justcallmekoko/ESP32DualBandWardriver/docs/images/GeoFencedScreen1.jpg

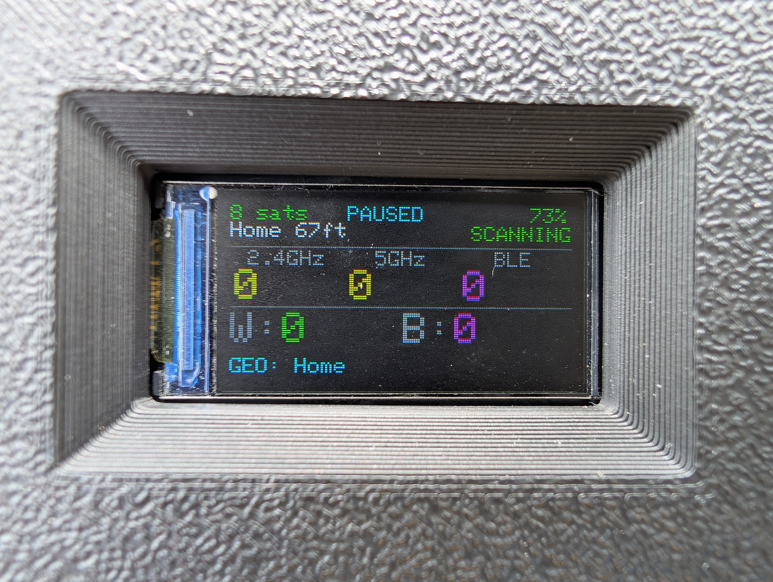
docs/images/GeoFencedScreen1.jpg
