justcallmekoko/ESP32DualBandWardriver/docs/images/WardrivingScreen1.jpg

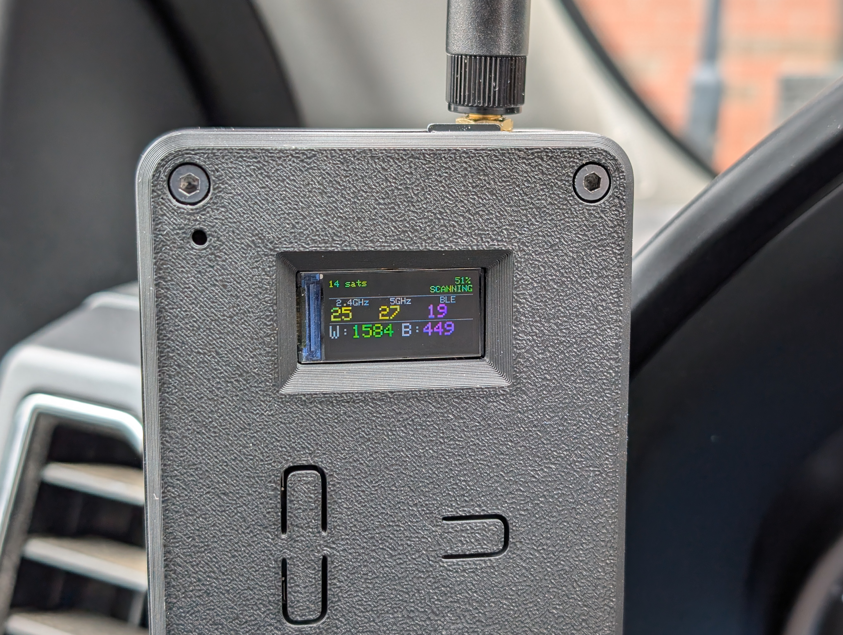
docs/images/WardrivingScreen1.jpg
