justcallmekoko/ESP32DualBandWardriver/docs/images/WebLogScreen.png

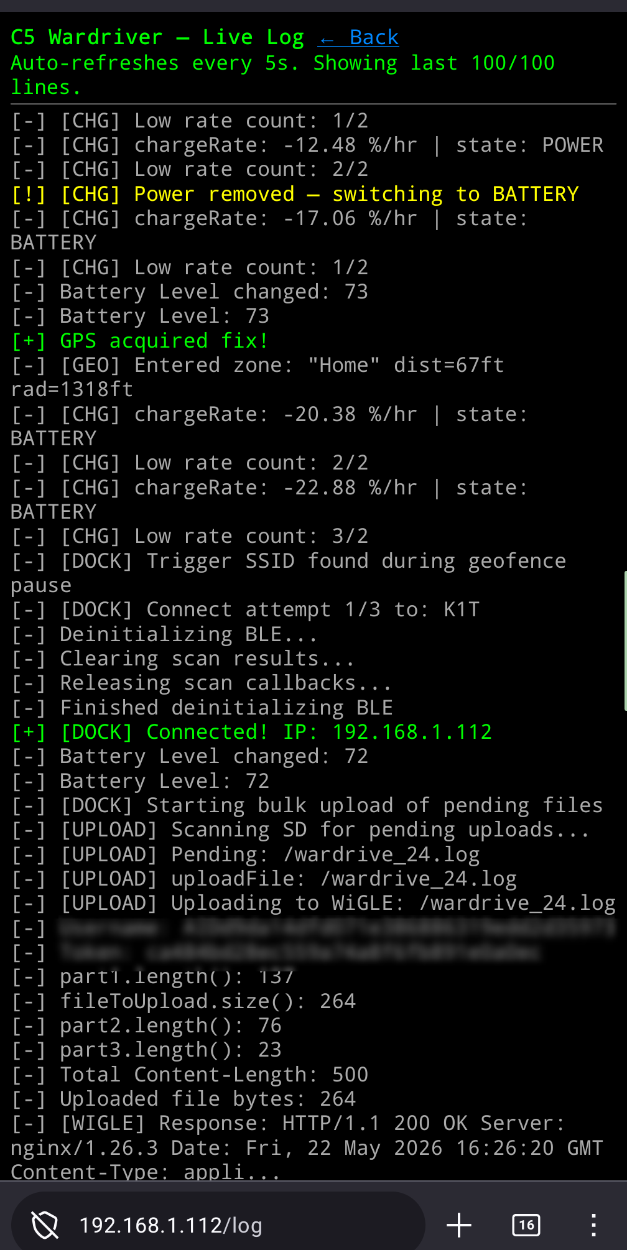
docs/images/WebLogScreen.png
