justcallmekoko/ESP32DualBandWardriver/src/Switches.h

#ifndef Switches_h
#define Switches_h

#include <Arduino.h>
#include "utils.h"

class Switches {
	private:
		int pin;
		uint32_t hold_lim;
		uint32_t cur_hold;
		
		uint32_t hold_init = millis();
		
		bool isheld;
		
		bool pullup;
		
		bool pressed;
		
		bool getButtonState();
		
	public:
		Switches();
		
		Switches(int pin, uint32_t hold_lim, bool pullup);
		
		int getPin();
		bool getPullup();
		
		bool justPressed();
		bool justReleased();
		bool isHeld();
};

#endif
