justcallmekoko/ESP32DualBandWardriver/src/utils.h

#pragma once
#ifndef utils_h
#define utils_h

#include <Arduino.h>
#include <vector>
#include <WiFi.h>
#include <LinkedList.h>

#include "configs.h"

#include "esp_heap_caps.h"
#include "mbedtls/base64.h"

struct mac_addr {
   unsigned char bytes[6];
};

struct Station {
  uint8_t mac[6];
  bool selected;
  uint16_t packets;
  uint16_t ap;
};

const char apple_ouis[][9] PROGMEM = {
  "00:17:F2", "00:1E:C2", "00:26:08", "F8:1E:DF", "BC:92:6B", 
  "28:E0:2C", "3C:07:54", "7C:D1:C3", "DC:A9:04", "F0:D1:A9",
  "C0:2C:5C", "00:03:93", "00:03:94", "00:03:95", "00:03:96",
  "00:03:97", "00:03:98", "00:03:99", "00:03:9A", "00:03:9B",
  "00:03:9C", "00:03:9D", "00:03:9E", "00:03:9F", "00:03:A0",
  "00:03:A1", "00:03:A2", "00:03:A3", "00:03:A4", "00:03:A5",
  "00:03:A6", "00:03:A7", "00:03:A8", "00:03:A9", "00:03:AA",
  "00:03:AB", "00:03:AC", "00:03:AD", "00:03:AE", "00:03:AF",
  "00:03:B0", "00:03:B1", "00:03:B2", "00:03:B3", "00:03:B4",
  "00:03:B5", "00:03:B6", "00:03:B7", "00:03:B8", "00:03:B9",
  "00:03:BA", "00:03:BB", "00:03:BC", "00:03:BD", "00:03:BE",
  "00:03:BF", "00:03:C0", "00:03:C1", "00:03:C2", "00:03:C3",
  "00:03:C4", "00:03:C5", "00:03:C6", "00:03:C7", "00:03:C8",
  "00:03:C9", "00:03:CA", "00:03:CB", "00:03:CC", "00:03:CD",
  "00:03:CE", "00:03:CF", "00:03:D0", "00:03:D1", "00:03:D2",
  "00:03:D3", "00:03:D4", "00:03:D5", "00:03:D6", "00:03:D7",
  "00:03:D8", "00:03:D9", "00:03:DA", "00:03:DB", "00:03:DC",
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
  "B4:B0:24", "C0:06:C3", "CC:68:B6", "E8:48:B8", "F0:A7:31"
};

const char xiaomi_ouis[][9] PROGMEM = {
  "04:CF:8C", "18:59:36", "38:1A:2D", "64:B4:73", "78:02:F8", 
  "90:4E:91", "C4:0B:CB", "D0:DB:32"
};

class Utils {
  public:
    uint8_t getDRAMUsagePercent();
    #ifdef HAS_PSRAM
      uint8_t getPSRAMUsagePercent();
    #endif
    String byteArrayToHexString(const std::vector<uint8_t>& byteArray);
    std::vector<uint8_t> hexStringToByteArray(const String& hexString);
    void generateRandomName(char *name, size_t length);
    const char* generateRandomName();
    void generateRandomMac(uint8_t* mac);
    String macToString(const Station& station);
    String macToString(uint8_t macAddr[6]);
    bool stringToMac(const char* macStr, uint8_t bytes[6]);
    static void macToStr(const uint8_t* mac, char* out18);
    void convertMacStringToUint8(const String& macStr, uint8_t macAddr[6]);
    const char* getManufacturer(const char *addr);
    String replaceOUIWithManufacturer(const char *sta_addr);
    IPAddress getNextIP(IPAddress currentIP, IPAddress subnetMask);
    uint16_t getNextPort(uint16_t port);
    String base64Encode(const String& input);
};

#endif
